OfficineEinstein/MakerLAB/Kc/MakerLAB_r011M/MakerLAB_r011M.png

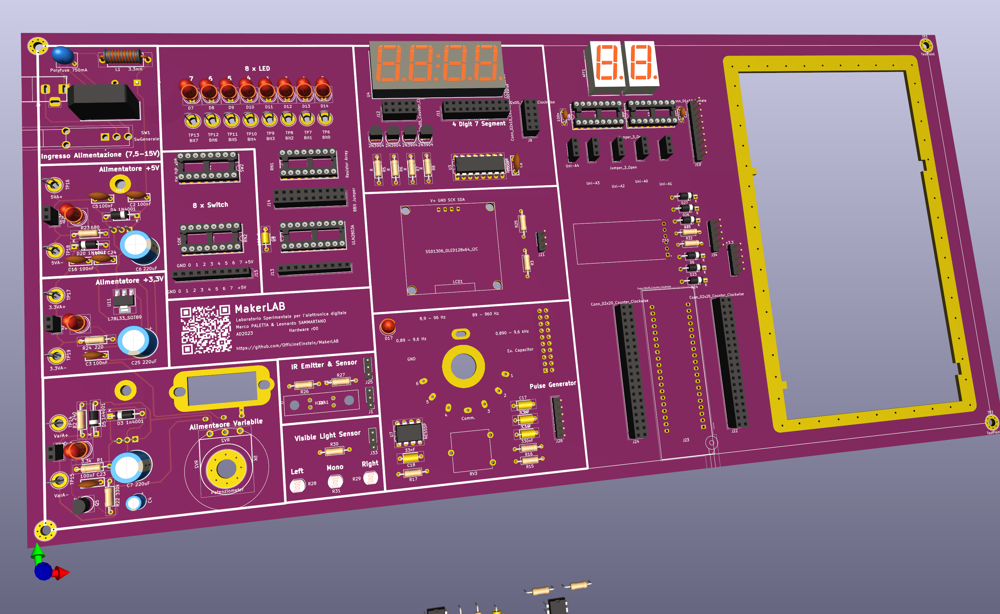
Kc/MakerLAB_r011M/MakerLAB_r011M.png
